Si-GCG/esp-32-touch-display-ashp-controller/heat-pump-project/includes/modbus_binary_sensors.yaml

# includes/modbus_binary_sensors.yaml

- platform: modbus_controller
  modbus_controller_id: aerona3
  name: "Weather Compensation Status"
  register_type: coil
  address: 2

- platform: modbus_controller
  modbus_controller_id: aerona3
  name: "Weather Compensation Zone 2 Status"
  register_type: coil
  address: 3

- platform: modbus_controller
  modbus_controller_id: aerona3
  name: "Cooling Weather Compensation Status"
  register_type: coil
  address: 5

- platform: modbus_controller
  modbus_controller_id: aerona3
  name: "Anti-legionella Function Status"
  register_type: coil
  address: 6

- platform: modbus_controller
  modbus_controller_id: aerona3
  name: "HP Unit Status"
  register_type: coil
  address: 7

- platform: modbus_controller
  modbus_controller_id: aerona3
  name: "Frost Protection Room Temperature Status"
  register_type: coil
  address: 8

- platform: modbus_controller
  modbus_controller_id: aerona3
  name: "Frost Protection Outdoor Temperature Status"
  register_type: coil
  address: 9

- platform: modbus_controller
  modbus_controller_id: aerona3
  name: "Frost Protection Outgoing Water Status"
  register_type: coil
  address: 10

- platform: modbus_controller
  modbus_controller_id: aerona3
  name: "DHW Storage Frost Protection Status"
  register_type: coil
  address: 11

- platform: modbus_controller
  modbus_controller_id: aerona3
  name: "Secondary Circuit Frost Protection Status"
  register_type: coil
  address: 12

- platform: modbus_controller
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

- platform: modbus_controller
  modbus_controller_id: aerona3
  name: "Terminal 45 Dehumidifier Status"
  register_type: coil
  address: 31

- platform: modbus_controller
  modbus_controller_id: aerona3
  name: "Terminal 46 DHW/Backup Heater Status"
  register_type: coil
  address: 32
